michaelNos/actuator-health/Doc1.docx

1. \Delta_t = 40\micro s. How Can I determine \Delta_t without chatgpt only with scope and basically find sampling, Nyquist, record duration and captured cycles after. The goal is to set sampling number before running and not running and then understand what is happening.
2. So, voltage that is going out of ACS724 OUT – voltage from IP- gives us residual noise. It means in ideal situation they should be equal? If yes, why? And why is the phase changing between them(CH1 and CH2)? And is it should be like that?
3. What is apparent transfer? As I know it is some kind of power.
4. How do I determine phase without chatgpt?
5. When are we sending impulse with frequency 1kHZ/10kHz we are basically sending AC current? Why would current change fast(10kHz) and slow(1kHz/100Hz)?
6. How can I analyze spectrum and harmonics manually with no chatgpt?
7. When we see highest voltage on fundamental harmonic and much lower voltages on 3d, 4th, 5th and so on harmonics does it mean that basically fundamental harmonic result is our wanted result and rest is noise that we don’t need?
8. Why does filtering increase phase lag?
9. What does it mean close to Nquist?
10. So basically, are we measuring OUT and IP- to calculate residual noise?
11. e(t) = V_measured - V_DC - V_1kHz. How to determine V_DC from AC signal without chatgpt, manualy?
12. How do I understand sine and cosine from the AFG?
13. What does -0.49 dB represent?
14. What is complex transfer phasor?
15. So internal filter of ACS724 allows only 15.5kHz signal to pass through?
16. So, is the phase different even when CH1 and CH2 are measuring the same? Why?
17. What H(10k)/H(1k) ratio telling us? And what ratio overall telling? And how to calculate it?
18. How to calculate propagation delay, response time, rise time?
19. Why RC = f/fc?
20. Why does delay contribute to phase shift?
