michaelNos/actuator-health/docs/evidence/raw/2026-09-07/bmp_20_002.bmp

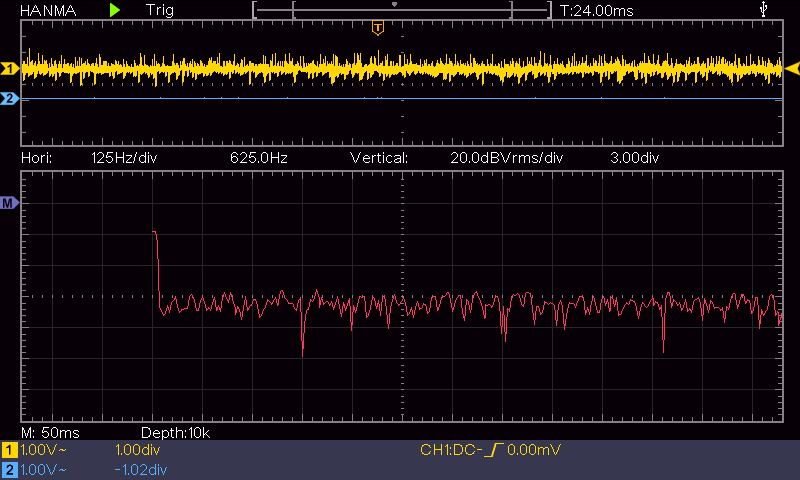
docs/evidence/raw/2026-09-07/bmp_20_002.bmp
