michaelNos/actuator-health/docs/04-measurement-chain-error-budget.md

# Phase 4 — Measurement-Chain Requirements and Error-Budget Allocation

**Status:** Design complete / baselined  
**Project:** Actuator Health Monitoring System

## Purpose

Phase 4 converts the accepted system requirements and ACS724 sensor design baseline into quantitative measurement-chain constraints for the later Analog Front End and ADC design phases.

This phase defines product-level requirements for signal range, accuracy allocation, useful resolution, bandwidth/anti-alias expectations, and measurement-valid versus electrical-survival behavior. It does **not** design the complete AFE, select final filter component values, configure ADC registers, or execute hardware measurements.

Under **DEV-001**, hardware-dependent quantities remain `TBD` where they cannot legitimately be established before implementation and verification.

## Accepted design inputs

The following inputs are already baselined by Phases 1–3 and are not reopened by Phase 4 unless a contradiction is found:

- valid Rev-1 current measurement range: **0 A to 5 A**, unidirectional;
- nominal ACS724 transfer at 5 V: `VOUT = 0.5 V + 0.8 V/A × I`;
- nominal sensor output span over the valid range: approximately **0.5 V to 4.5 V**;
- sensor output is supply-dependent/ratiometric and actual offset/sensitivity are calibration parameters;
- required diagnostic signal band: **DC to 10 kHz**;
- nominal acquisition target: **100 kS/s**;
- Nyquist frequency at 100 kS/s: **50 kHz**;
- system current-accuracy target after calibration: **≤ ±0.10 A**;
- stretch current-accuracy target: **±0.05 A**;
- reported current-resolution target: **≤ 10 mA**;
- the stock ACS724 carrier bandwidth is approximately **90 kHz**, so the AFE must provide deliberate anti-alias filtering;
- values outside 0–5 A shall not be treated as calibrated valid measurements merely because the sensor or downstream electronics may still produce a voltage.

## 4.1 — Measurement-chain signal range, headroom and overrange

### MEAS-001 — Preserve the native ACS724 signal span

**Status:** Accepted

Rev-1 shall preserve approximately unity DC/passband gain from the ACS724 through the Analog Front End rather than deliberately amplifying or compressing the sensor output solely to occupy more ADC range.

The nominal valid sensor range therefore remains approximately:

- `0 A → 0.5 V`;
- `5 A → 4.5 V`.

For a nominal 0–5 V ADC input range this leaves approximately **0.5 V nominal headroom at each rail**.

The later AFE/ADC design shall ensure that expected sensor, supply, AFE and component variation does not cause clipping within the valid **0–5 A** measurement range.

Values corresponding to current outside the calibrated 0–5 A range may still produce an ADC code, but shall be treated as **overrange / invalid measurement**, not as valid extrapolated current.

Near-rail or saturated ADC conditions shall be detectable by the later firmware as measurement overrange/saturation.

Electrical survival remains distinct from measurement validity. The later AFE/protection design shall prevent plausible abnormal sensor/transient voltages from damaging the ADC input, but exact clamp/protection circuitry is deferred to the appropriate later design phases.

Measured `Voffset`, sensitivity and practical rail margin remain verification-stage quantities and shall not be invented during Phase 4.

### Rationale

The native ACS724 span already uses approximately 4 V of a nominal 5 V ADC range. Additional analog scaling would provide limited resolution benefit while adding gain/offset error and reducing headroom. Preserving the native span therefore gives a simpler and more robust Rev-1 measurement chain.

## 4.2 — Accuracy allocation and useful resolution

### MEAS-002 — Measurement-chain error and resolution budget

**Status:** Accepted

The Phase 1 system current-accuracy requirement of **≤ ±0.10 A after calibration** corresponds nominally, at `S ≈ 0.8 V/A`, to an equivalent full-chain voltage error allowance of:

`0.10 A × 0.8 V/A = 80 mV`

Rev-1 shall use the following conservative worst-case design allocation:

| Contributor | Current-domain allocation | Nominal voltage equivalent |
|---|---:|---:|
| Sensor + calibration residual | ±50 mA | ±40 mV |
| AFE residual error | ±15 mA | ±12 mV |
| ADC/reference residual error | ±10 mA | ±8 mV |
| Noise contribution | ±10 mA | ±8 mV |
| Supply/temperature and other residual effects | ±15 mA | ±12 mV |
| **Worst-case total** | **±100 mA** | **±80 mV** |

These values are **design allocations**, not claims of measured performance. In particular, the individual ACS724 sensor's residual error after calibration, practical noise, supply effects and temperature behavior remain `TBD` until implementation and verification.

The allocation is intentionally conservative and additive so that later subsystem designs receive explicit error limits. Where contributors are statistically independent, later analysis may additionally evaluate root-sum-square uncertainty, but statistical combination shall not be used during design to hide violation of an allocated worst-case limit.

The Phase 1 **±0.05 A stretch target** is not guaranteed by this baseline. It may be claimed only if later measured/calibrated system performance demonstrates it.

### Useful resolution requirement

The accepted reported-current resolution target is **≤10 mA**. At nominal sensor sensitivity:

`10 mA × 0.8 V/A = 8 mV`

The ADC-facing measurement chain shall therefore provide **effective usable voltage resolution of 2 mV or better** under the intended acquisition conditions. Nominally this corresponds to:

`2 mV / 0.8 V/A = 2.5 mA`

This provides approximately fourfold margin below the 10 mA reported-current step.

The 2 mV requirement is an **effective chain/ADC-domain performance requirement**, not merely a converter-LSB calculation. Phase 6 shall verify that quantization, ADC noise, reference/supply behavior and acquisition conditions provide this useful performance at the selected sample rate.

Resolution and accuracy remain distinct: a chain may resolve changes smaller than 10 mA while still carrying larger systematic measurement error.

### Rationale

The sensor receives the largest accuracy allocation because its residual offset/gain behavior, temperature dependence and calibration residual are expected to dominate more strongly than the downstream AFE or ADC. The 2 mV useful-resolution requirement prevents nominal ADC bit depth from being mistaken for practical measurement capability and leaves adequate margin for stable 10 mA reporting.

## 4.3 — Bandwidth and anti-alias requirement handoff

### MEAS-003 — Preserve the diagnostic band and attenuate Nyquist-region content

**Status:** Accepted

The Rev-1 measurement chain shall preserve the complete **DC to 10 kHz** diagnostic signal band while using the nominal **100 kS/s** acquisition rate.

The Analog Front End shall include deliberate low-pass anti-alias filtering before ADC conversion. The stock ACS724 carrier FILTER network is not sufficient by itself to satisfy this requirement.

Phase 5 shall design the anti-alias response to meet the following measurement-chain targets:

- attenuation at **10 kHz**: **≤1 dB** relative to the low-frequency/passband response;
- attenuation at **50 kHz** (the Nyquist frequency at 100 kS/s): **≥20 dB** relative to the low-frequency/passband response.

Equivalently:

`|H(10 kHz)| ≥ -1 dB`

`|H(50 kHz)| ≤ -20 dB`

The exact filter topology, order, cutoff frequency and component values are intentionally deferred to Phase 5, where these targets shall be reconciled with component tolerances, AFE error allocation, ADC drive requirements and available hardware.

The resulting implemented frequency response shall later be verified experimentally. Frequencies above Nyquist that are insufficiently attenuated can alias into the sampled spectrum and cannot in general be removed afterward by digital processing.

### Rationale

A 100 kS/s sample rate gives a 50 kHz Nyquist frequency, but Nyquist alone does not prevent aliasing. The accepted diagnostic band ends at 10 kHz, leaving a 10–50 kHz transition region in which the analog filter can roll off. Specifying passband preservation and a Nyquist-region attenuation target gives Phase 5 a quantitative design objective without prematurely choosing the filter implementation.

## Phase 4 completion direction

MEAS-001 through MEAS-003 now define the principal measurement-chain constraints needed by the AFE and ADC design phases. Phase 4 shall close with a compact specification summary, traceability, verification handoff and explicit list of hardware-dependent `TBD` quantities; those consolidation items do not create additional product behavior unless a new engineering choice is identified.

## Planned Phase 4 output

Phase 4 will close with a compact measurement-chain specification containing:

- ADC-facing signal-range/headroom requirement;
- quantitative current and voltage error-budget allocation;
- minimum useful resolution/noise requirement;
- bandwidth and anti-alias handoff to Phase 5;
- overrange/rail behavior requirements;
- explicit `TBD` items to be measured later;
- traceability to the accepted Phase 1–3 inputs.

Only explicitly approved Phase 4 engineering decisions are baselined.
