michaelNos/actuator-health/Schematics/RCfilter/RCfilter.kicad_sch

## KiCad design Schematics/RCfilter/RCfilter.kicad_sch (2026-09-14)

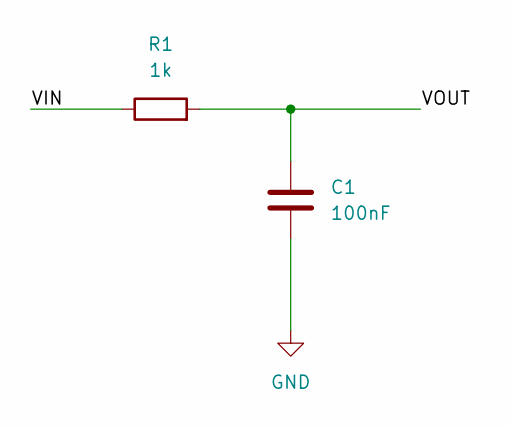
[picture p8: schematic RCfilter.kicad_sch]

Parts:
C1: 100nF
R1: 1k

Connections:
GND: C1.2
VIN: R1.1
VOUT: C1.1, R1.2
