michaelNos/actuator-health/Schematics/actuator-health/actuator-health.kicad_sch

## KiCad design Schematics/actuator-health/actuator-health.kicad_sch (2026-10-05, an earlier design)

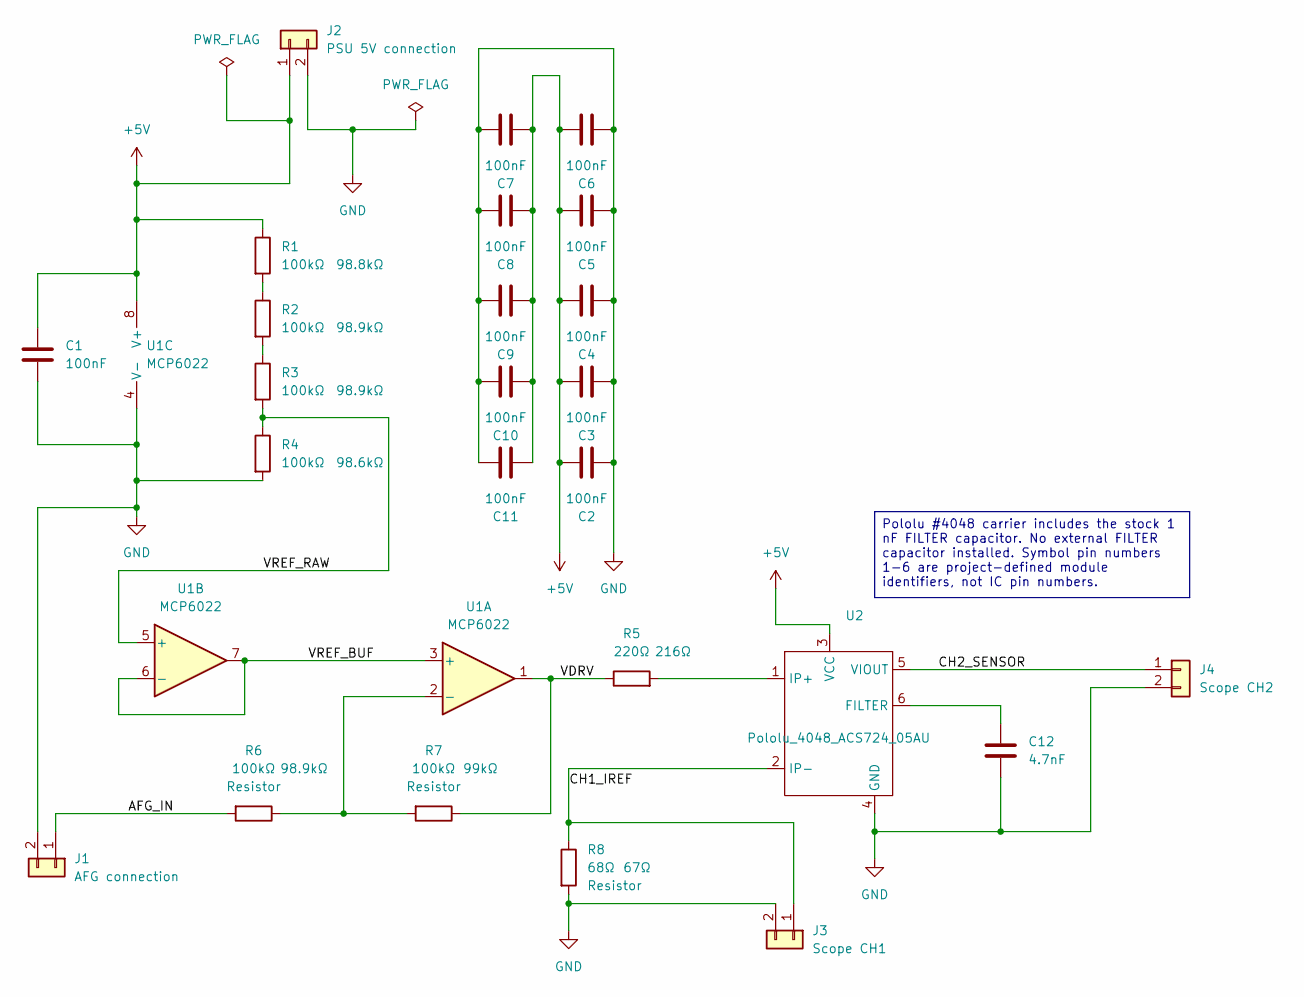
[picture p9: schematic actuator-health.kicad_sch]

Parts:
C1, C2, C3, C4, C5, C6, C7, C8, C9, C10, C11: 100nF
C12: 4.7nF
J1: AFG connection
J2: PSU 5V connection
J3: Scope CH1
J4: Scope CH2
R1, R2, R3, R4, R6, R7: 100kΩ
R5: 220Ω
R8: 68Ω
U1: MCP6022
U2: Pololu_4048_ACS724_05AU

Connections:
+5V: C1.1, C2.2, C3.2, C4.2, C5.2, C6.2, C7.1, C8.1, C9.1, C10.1, C11.1, J2.1, R1.1, U1.8 (V+), U2.3 (VCC)
AFG_IN: J1.1, R6.2
CH1_IREF: J3.1, R8.1, U2.2 (IP-)
CH2_SENSOR: J4.1, U2.5 (VIOUT)
GND: C1.2, C2.1, C3.1, C4.1, C5.1, C6.1, C7.2, C8.2, C9.2, C10.2, C11.2, C12.2, J1.2, J2.2, J3.2, J4.2, R4.2, R8.2, U1.4 (V-), U2.4 (GND)
unnamed: C12.1, U2.6 (FILTER)
unnamed: R1.2, R2.1
unnamed: R2.2, R3.1
unnamed: R5.2, U2.1 (IP+)
unnamed: R6.1, R7.2, U1.2 (-)
VDRV: R5.1, R7.1, U1.1
VREF_BUF: U1.3 (+), U1.6 (-), U1.7
VREF_RAW: R3.2, R4.1, U1.5 (+)

Notes on the sheet:
Pololu #4048 carrier includes the stock 1 nF FILTER capacitor. No external FILTER capacitor installed. Symbol pin numbers 1-6 are project-defined module identifiers, not IC pin numbers.
